veter-team/a20/cad/models/base/stl/base1.stl

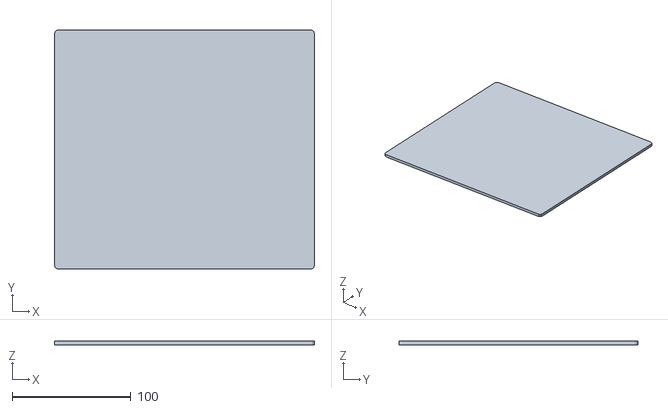
[picture p18: CAD file, 2014-09-18]
cad/models/base/stl/base1.stl
219.2 x 201.6 x 3.00
