veter-team/a20/cad/for3dprint/base/front_pannel.stl

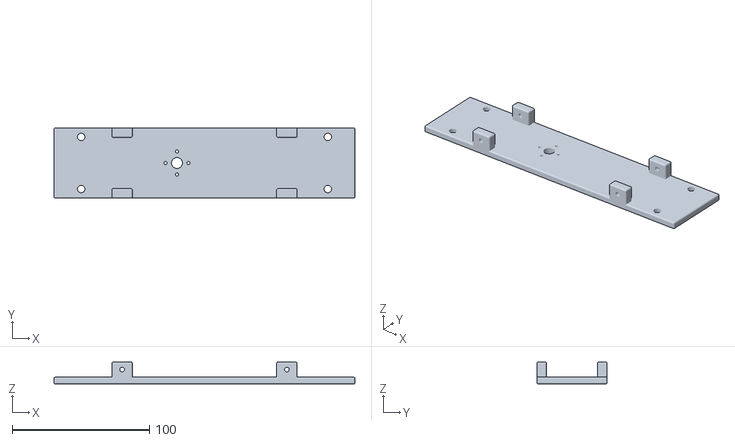
[picture p19: CAD file, 2014-09-14]
cad/for3dprint/base/front_pannel.stl
219.2 x 51.2 x 16.0
