veter-team/a20/cad/models/base/wheel.scad

include <../main_dimensions.scad>
use <tire.scad>
use <rim.scad>


module wheel()
{
    tire();
    color("Gainsboro")
    rim();
}


if(ASSEMBLY == undef || ASSEMBLY == 0)
{
  wheel();
}
