veter-team/a20/cad/models/main_dimensions.scad

use <MCAD/metric_fastners.scad>


tolerance = 0.4;

// Maximal robot footprint is DIN A3 - 210 * 2 x 297 = 420 x 297
// http://piwars.org/?page_id=16
// Let us make the robot large enough but not on the limit
allowed_x_size = 420 - 10;
allowed_y_size = 297 - 10;

shaft_radius = 6 / 2 + tolerance / 2;

//wheel_radius = 128 / 2;
//wheel_width = 58;
//wheel_radius = 100 / 2;
//wheel_width = 42;
wheel_radius = 125 / 2;
wheel_width = 65;

half_rim_width = 25;

hub_outer_radius = 25.4 / 2 + tolerance / 2;
hub_inner_radius = 12 / 2 + tolerance / 2;
hub_height1 = 5;
hub_height2 = 4.5;

motor_holder_x_dim = 43.05;
motor_holder_y_dim = 19.05 * 2;
motor_holder_z_dim = 44;
motor_holder_h = 3;

motor_shaft_shift = 7;

radial_bearing_r = 19 / 2 + tolerance / 2;
radial_bearing_h = 6 + tolerance * 2;

//shaft_shift = 20.3 + motor_shaft_shift;
shaft_shift = 25 + motor_shaft_shift;

shaft_coupling_l = 16;

belt_gear_15_r1 = 14;
belt_gear_15_r2 = 24 / 2;
belt_gear_15_l1 = 14;
belt_gear_15_l = 20;

belt_gear_10_r1 = 23 / 2;
belt_gear_10_r2 = 16 / 2;
belt_gear_10_l1 = 14;
belt_gear_10_l = 20;

// To simplify switching between two gear types
//belt_gear_r1 = belt_gear_10_r1;
//belt_gear_r2 = belt_gear_10_r2;
//belt_gear_l1 = belt_gear_10_l1;
//belt_gear_l = belt_gear_10_l;

belt_gear_r1 = belt_gear_15_r1;
belt_gear_r2 = belt_gear_15_r2;
belt_gear_l1 = belt_gear_15_l1;
belt_gear_l = belt_gear_15_l;

wheel_holder_x_dim = 40;
// belt_gear_l + 1 * 2 -> 1mm distance from inner wals 
// 2 * 2 = two inner walls of 2mm
wheel_holder_y_dim = belt_gear_l + 1 * 2 + radial_bearing_h * 2 + 2 * 2;
wheel_holder_z_dim = 38;

front_pannel_h = 5;
front_pannel_z_dim = wheel_holder_z_dim + (shaft_radius + 2) + 8;

akku_x_dim = 134;
akku_y_dim = 67;
akku_z_dim = 61;

akku_belt_hole_w = 22;
base_bottom_battery_holder_dim = [akku_x_dim - 2 * 20, 10, 15];

//base_x_size = allowed_x_size - wheel_width * 2 - 60;
base_x_size = akku_x_dim + 2 * wheel_holder_y_dim + 6;
base_y_size = ((330.5 - 2 * 3.1415 * belt_gear_r2) / 2 / 2 + shaft_shift) * 2 + front_pannel_h * 2;
base_z_size = 3;

holder_shaft_r = 5 / 2 + tolerance / 2;

md22_dim = [110, 51, 1.5];

cover2_h = 25 + 1;
cover1_h = cover2_h + 20 + 5;


mount_hole_radius = 3 / 2 + tolerance / 2;

ball_r = 70 / 2;
rotor_r = 76 / 2;
blade_w = base_x_size + 2 * wheel_width;


module mounting_hole(thickness, use_bolt)
{
    d = 3 + tolerance;
    l = thickness;
    
    if(use_bolt)
    {
        csk_bolt(d, l + 0.6 * d);
    }
    else
    {
        cylinder(h = l, r = d / 2);
    }
    rotate([180, 0, 0]) cylinder(h = l, r = 1.0 * d);
    translate([0, 0, thickness]) cylinder(h = l, r = 1.0 * d);
}
