veter-team/a20/cad/models/deck2/cover1.scad

use <cover_base.scad>
include <../main_dimensions.scad>


module cover1()
{
    cover_base(cover1_h, base_y_size / 2 + 20);
}


if(ASSEMBLY == undef || ASSEMBLY == 0)
{
    translate([0, -20 + (base_y_size / 2 + 20) / 2, cover1_h + 5])
    rotate([0, 180, 0])
    cover1();
}
