veter-team/a20/cad/models/accessories/ball_collector/bearing_cover.scad

use <ball_collector_blade.scad>


if(ASSEMBLY == undef || ASSEMBLY == 0)
{
    rotate([0, 90, 0])
    bearing_cover();
}
